impatrq/Protorp/Compras/Facturas de compra/20251116_184129.jpg

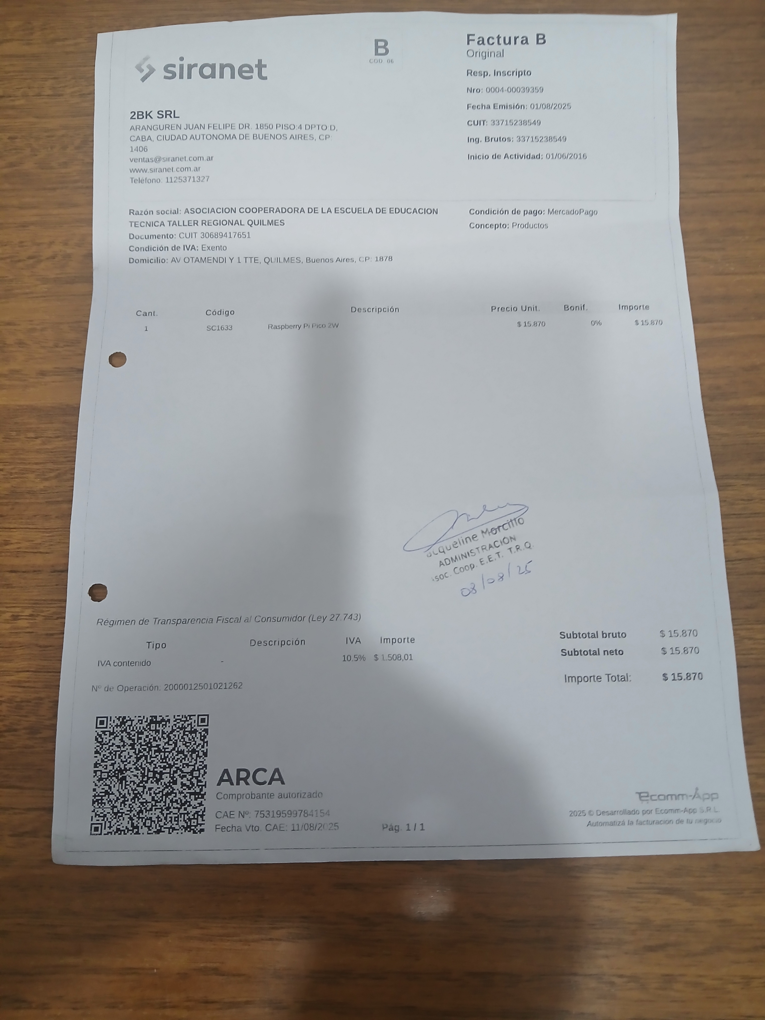
Compras/Facturas de compra/20251116_184129.jpg
