impatrq/Protorp/Compras/Facturas de compra/20251116_184212.jpg

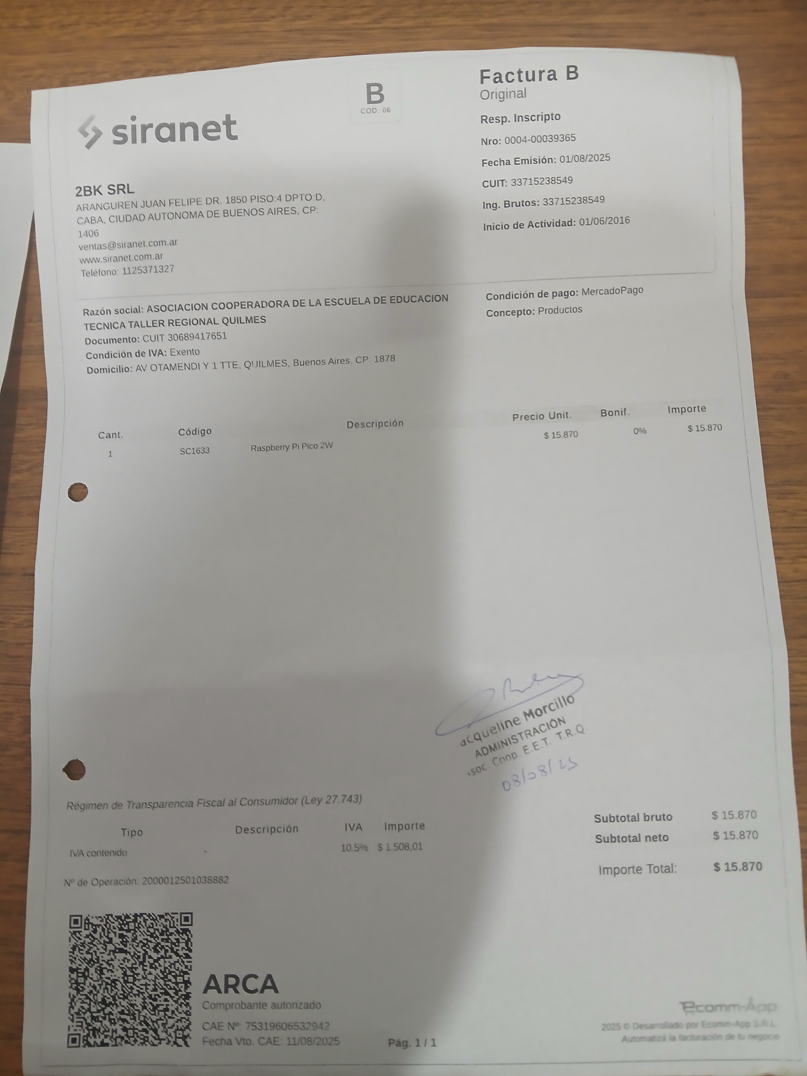
Compras/Facturas de compra/20251116_184212.jpg
