impatrq/Protorp/Compras/Facturas de compra/20251116_184254.jpg

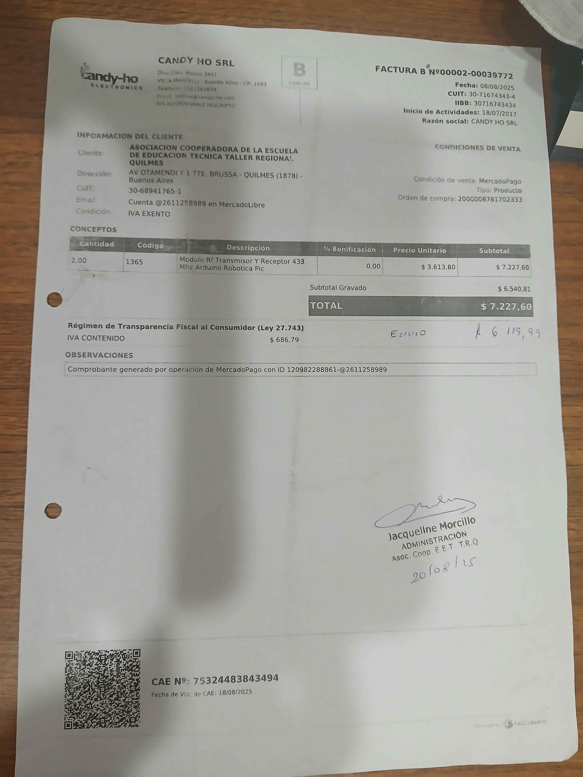
Compras/Facturas de compra/20251116_184254.jpg
