impatrq/Protorp/Compras/Facturas de compra/20251116_184328.jpg

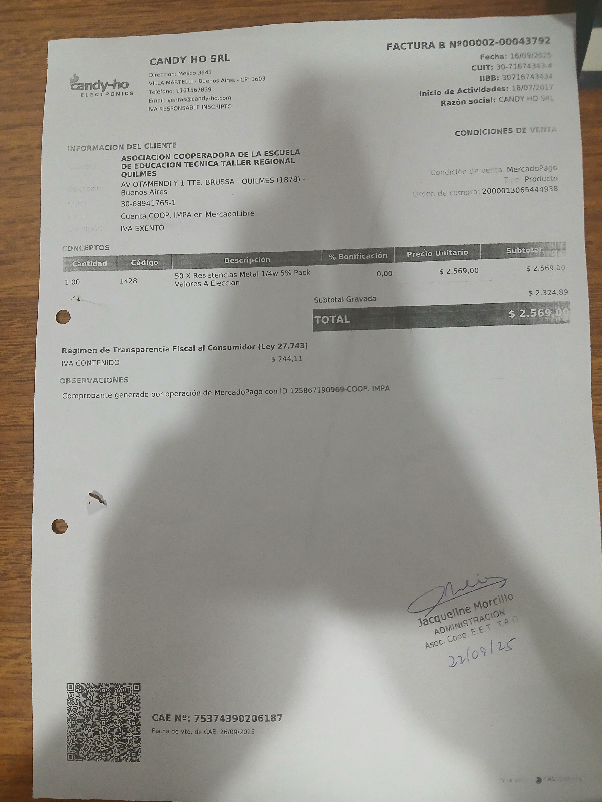
Compras/Facturas de compra/20251116_184328.jpg
