impatrq/Protorp/Compras/Facturas de compra/20251116_184347.jpg

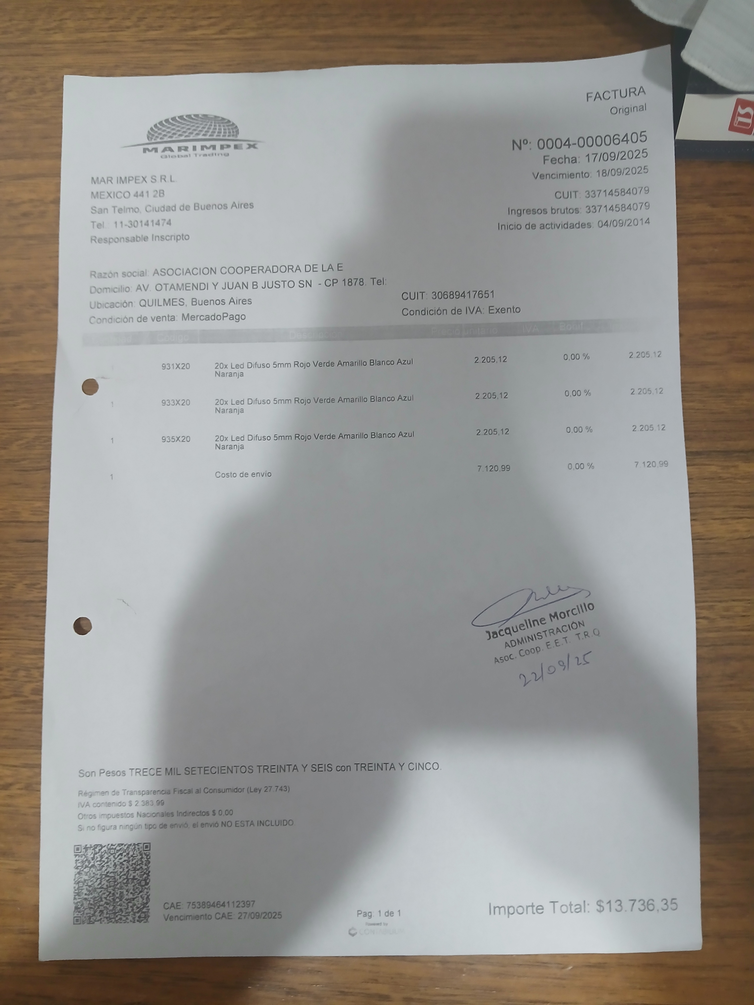
Compras/Facturas de compra/20251116_184347.jpg
