impatrq/Protorp/Compras/Facturas de compra/20251116_184413.jpg

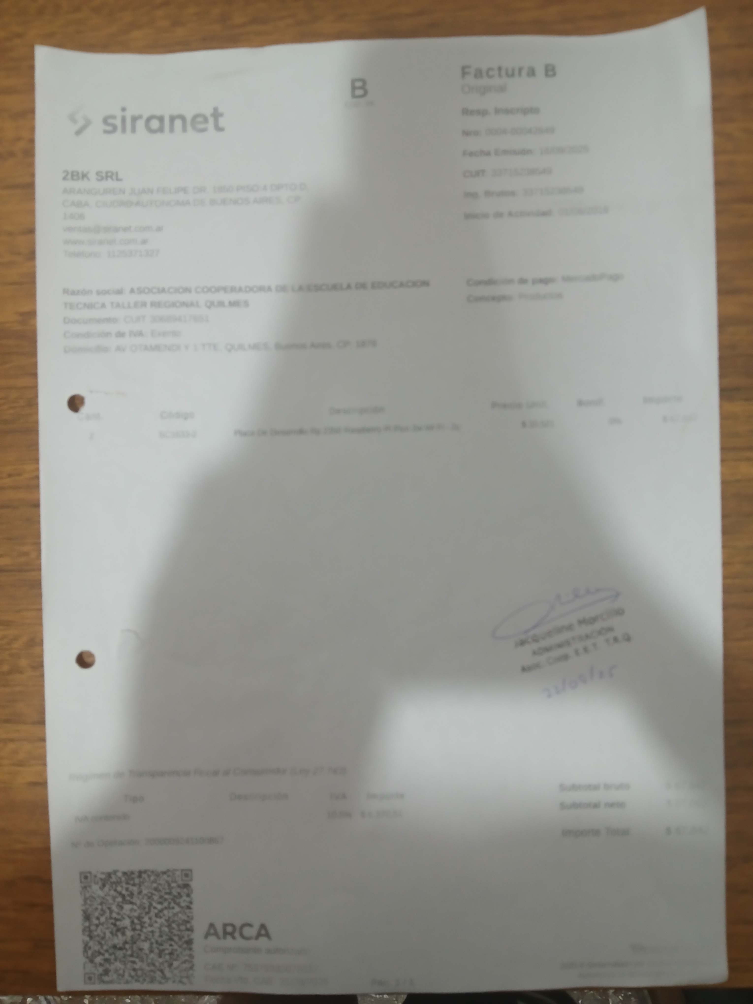
Compras/Facturas de compra/20251116_184413.jpg
