impatrq/Protorp/Compras/Facturas de compra/20251116_184430.jpg

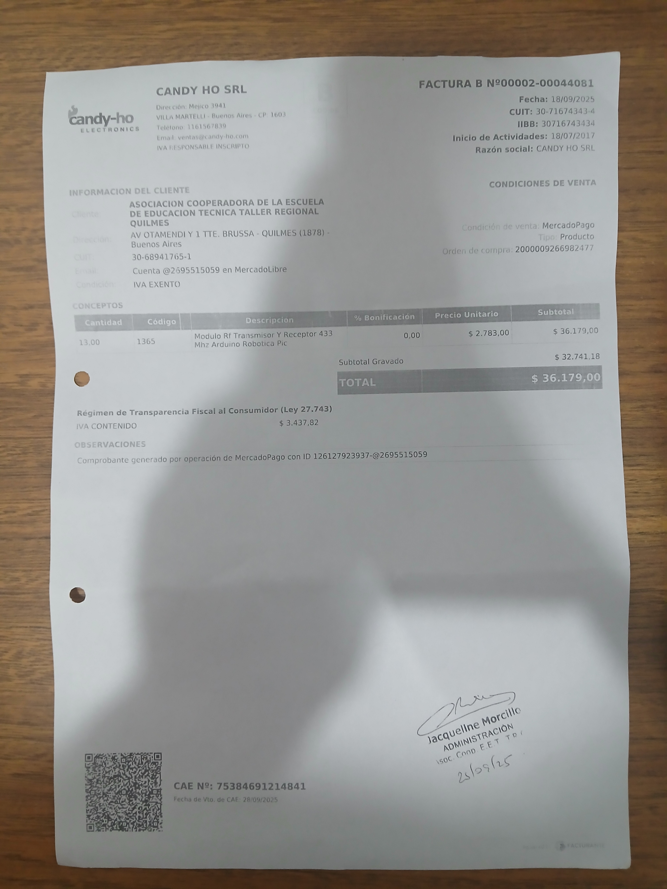
Compras/Facturas de compra/20251116_184430.jpg
