impatrq/Protorp/Compras/Facturas de compra/20251116_184449.jpg

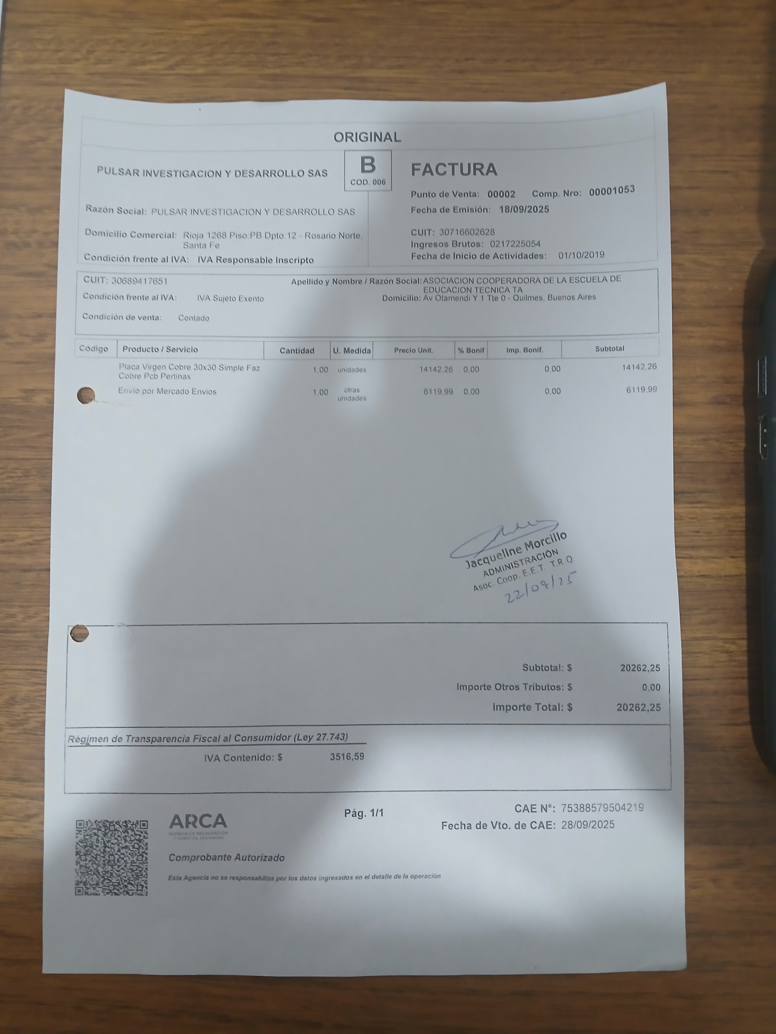
Compras/Facturas de compra/20251116_184449.jpg
