impatrq/Protorp/Compras/Facturas de compra/20251116_184504.jpg

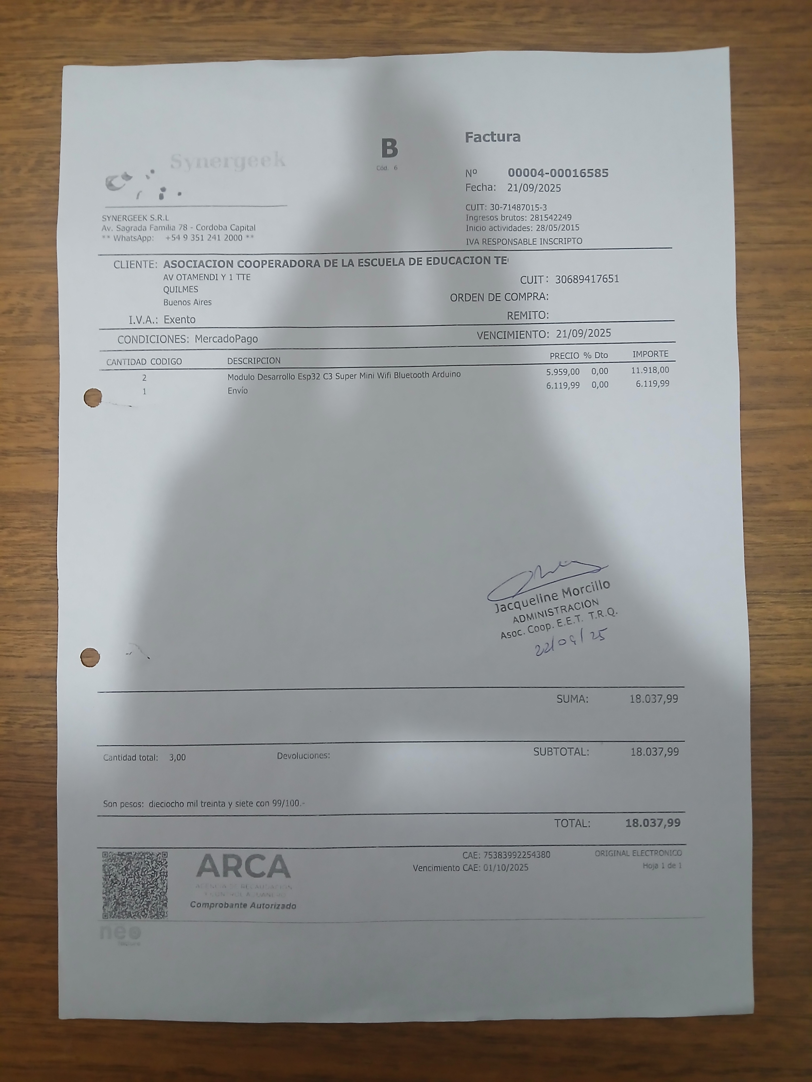
Compras/Facturas de compra/20251116_184504.jpg
