impatrq/Protorp/Compras/Facturas de compra/20251116_184520.jpg

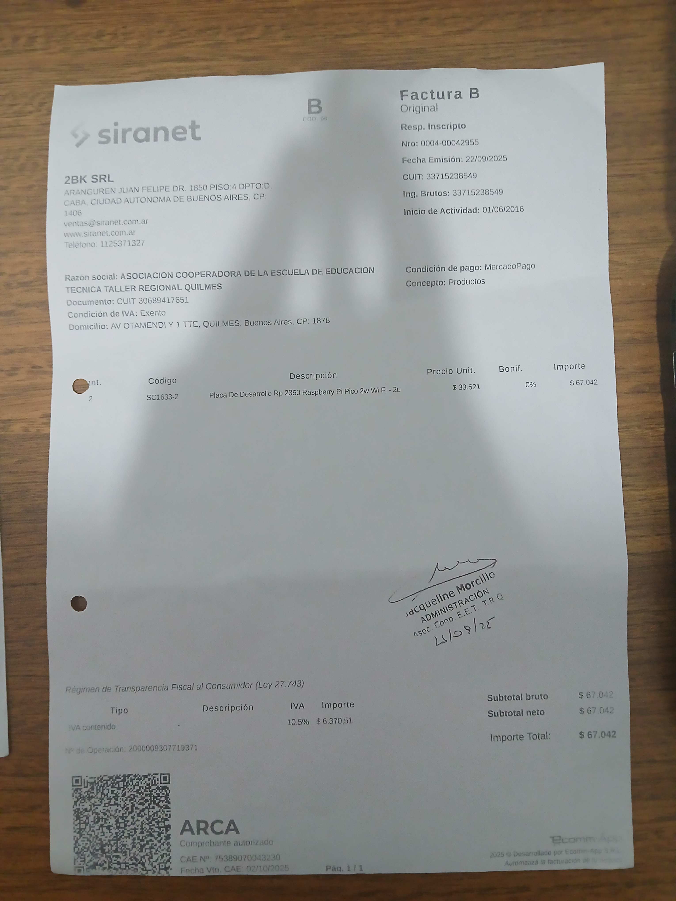
Compras/Facturas de compra/20251116_184520.jpg
