impatrq/Protorp/Compras/Facturas de compra/20251116_184534.jpg

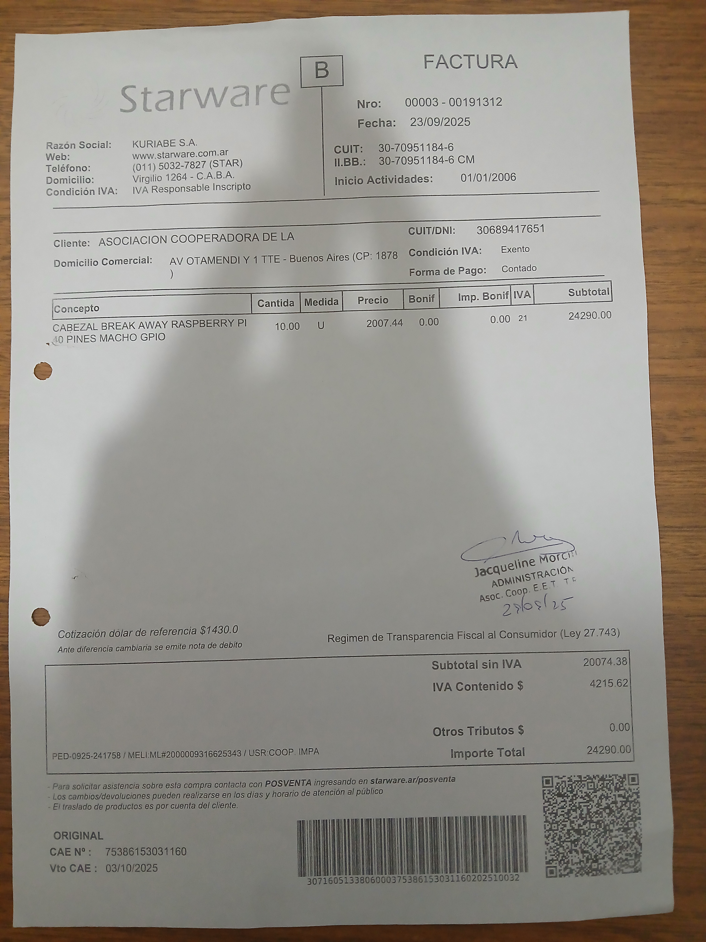
Compras/Facturas de compra/20251116_184534.jpg
