impatrq/Protorp/Equipo/CVs del equipo/CV - Joaquin.jpg

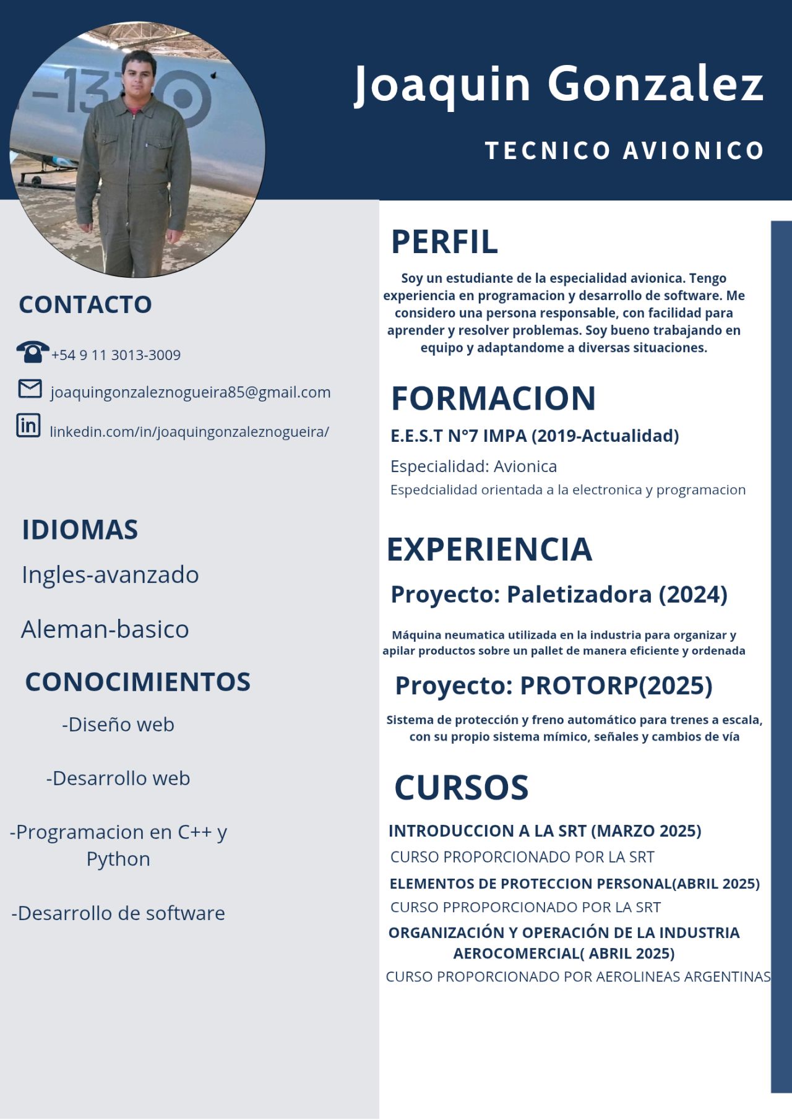
Equipo/CVs del equipo/CV - Joaquin.jpg
