impatrq/Protorp/Equipo/Foto del equipo/Foto del eqipo.jpeg

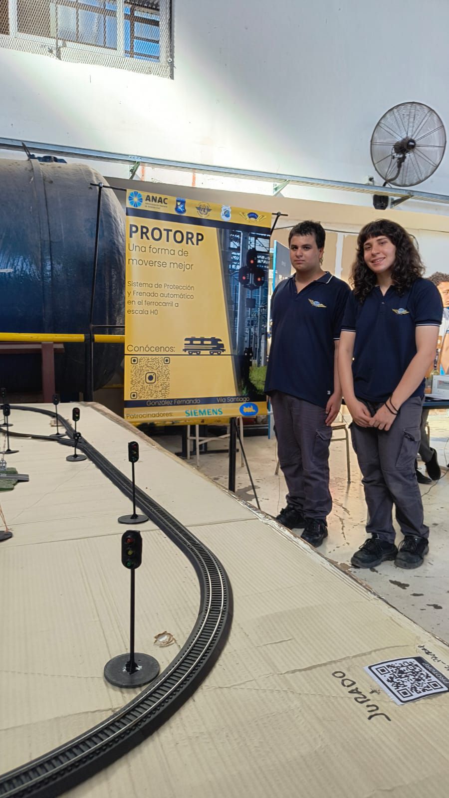
Equipo/Foto del equipo/Foto del eqipo.jpeg
