impatrq/Protorp/fotos/diagramas/prototipo 1 diagrama electrico.webp

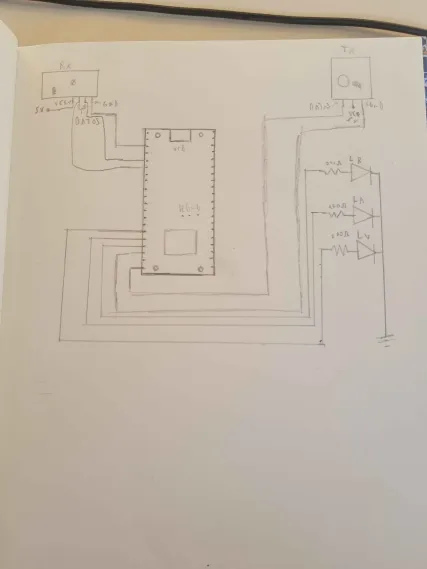
fotos/diagramas/prototipo 1 diagrama electrico.webp
