impatrq/Protorp/fotos/impresiones 3D/9bde5b57-a3d0-4a50-99e6-3efff3342a33.jpg

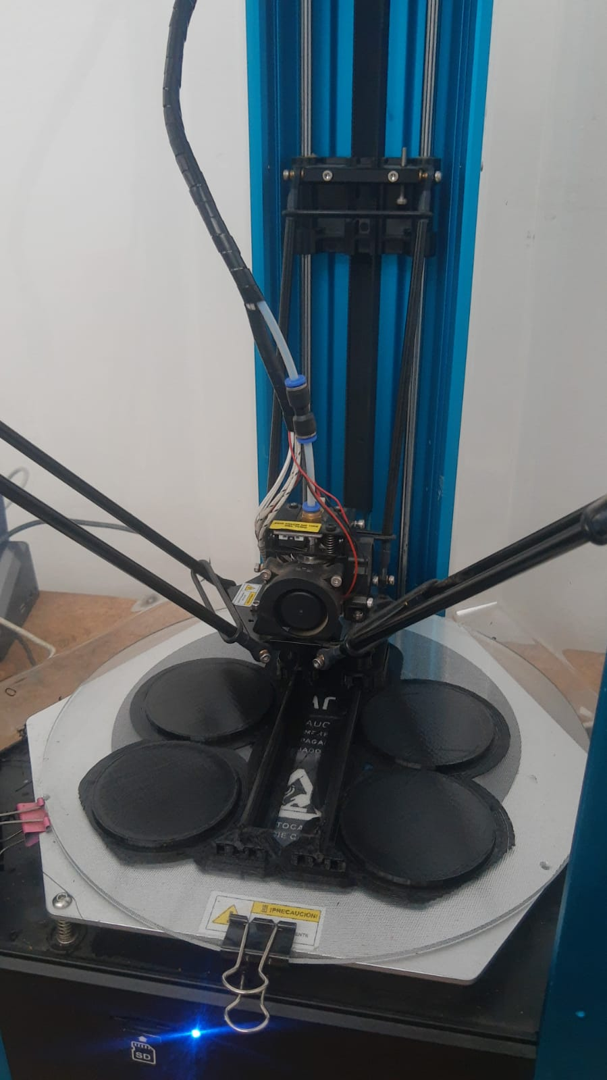
fotos/impresiones 3D/9bde5b57-a3d0-4a50-99e6-3efff3342a33.jpg
