impatrq/Protorp/fotos/impresiones 3D/df6539c7-ce4e-4fce-84c8-1d385a50d44c.jpg

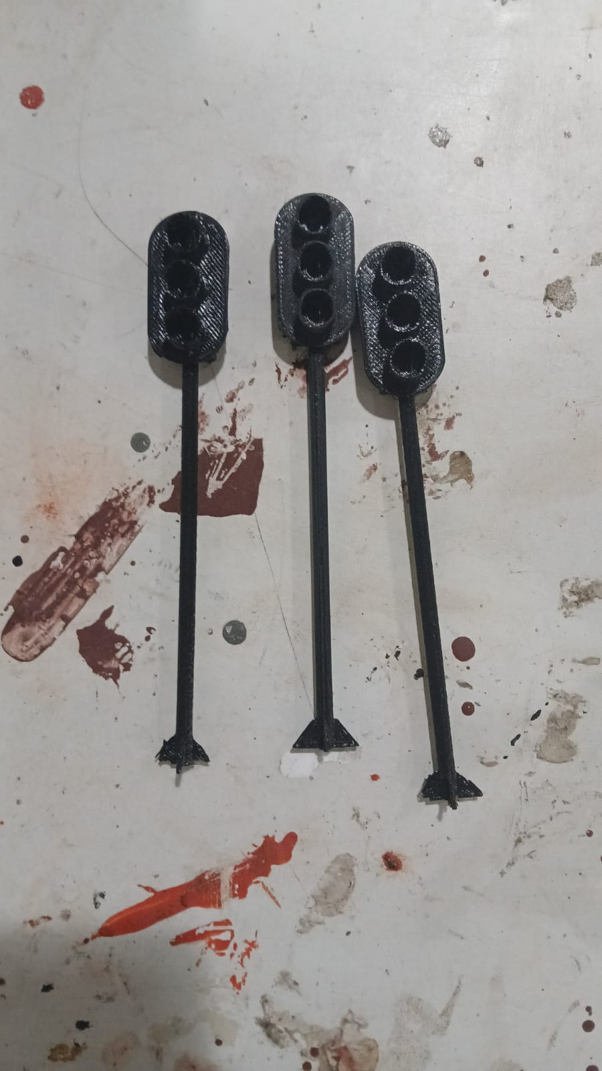
fotos/impresiones 3D/df6539c7-ce4e-4fce-84c8-1d385a50d44c.jpg
