impatrq/Protorp/fotos/Maqueta/IMG-20251118-WA0002.jpg

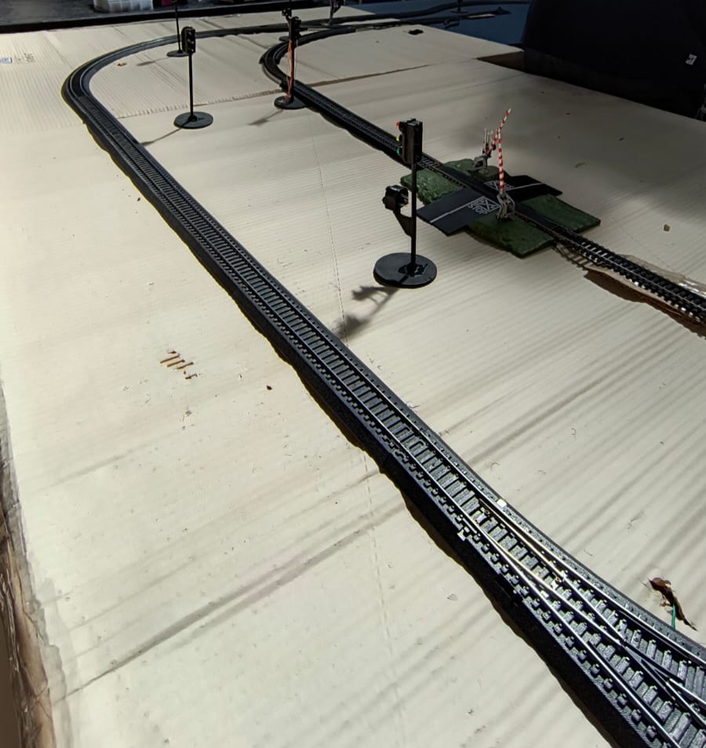
fotos/Maqueta/IMG-20251118-WA0002.jpg
