impatrq/Protorp/fotos/Maqueta/IMG-20251118-WA0003.jpg

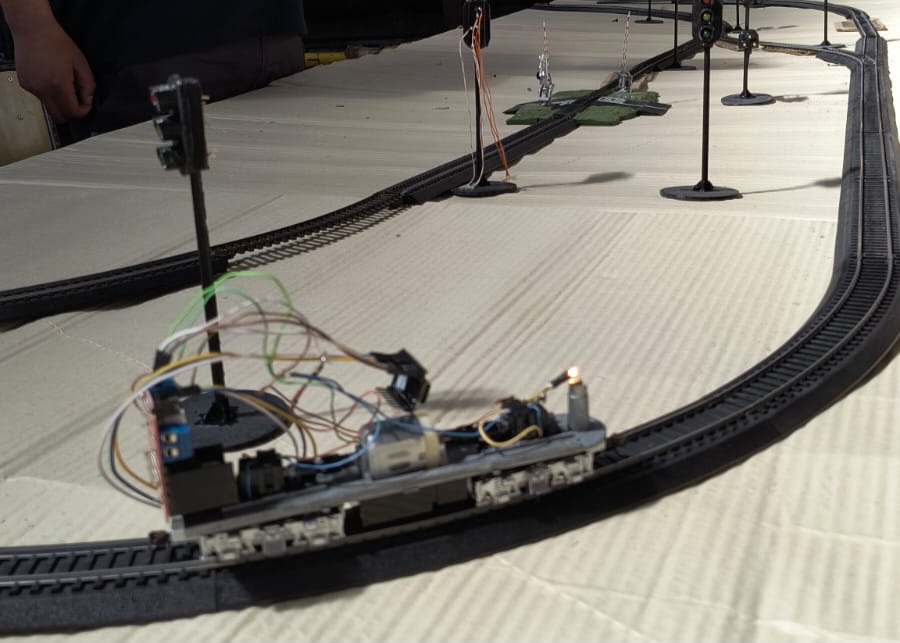
fotos/Maqueta/IMG-20251118-WA0003.jpg
