impatrq/Protorp/fotos/Maqueta/IMG-20251118-WA0004.jpg

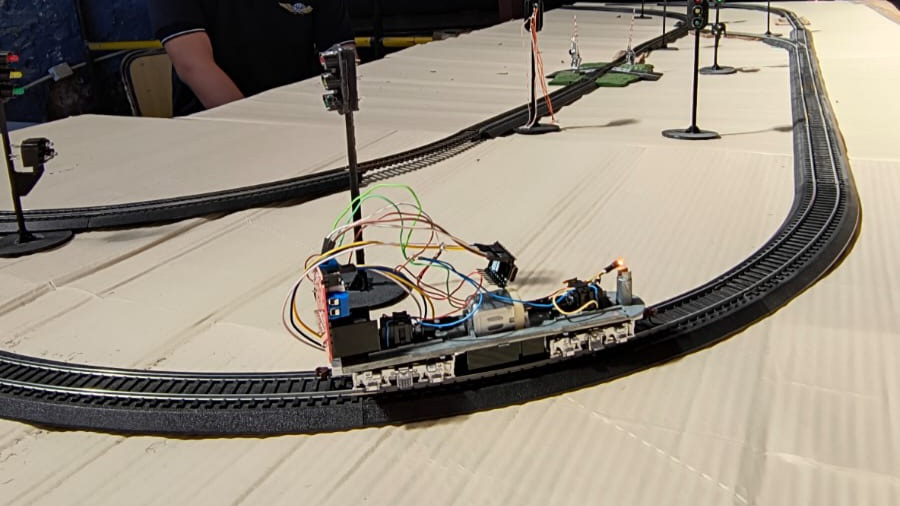
fotos/Maqueta/IMG-20251118-WA0004.jpg
