impatrq/Protorp/fotos/placas de cobre/6936b12a-9ef0-415d-9e3a-1d418f14f2b1.jpg

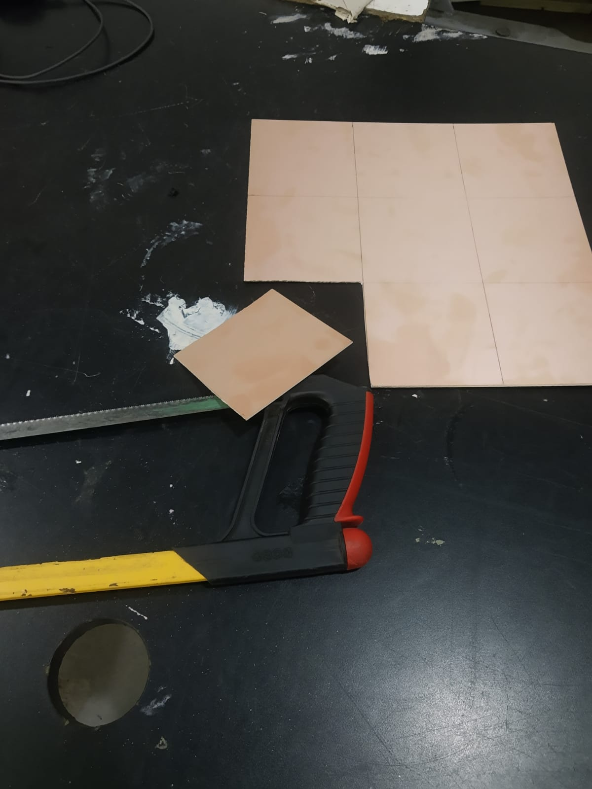
fotos/placas de cobre/6936b12a-9ef0-415d-9e3a-1d418f14f2b1.jpg
