impatrq/Protorp/fotos/placas de cobre/2706066d-67e2-4fa1-b246-8f61f098e9b2.jpg

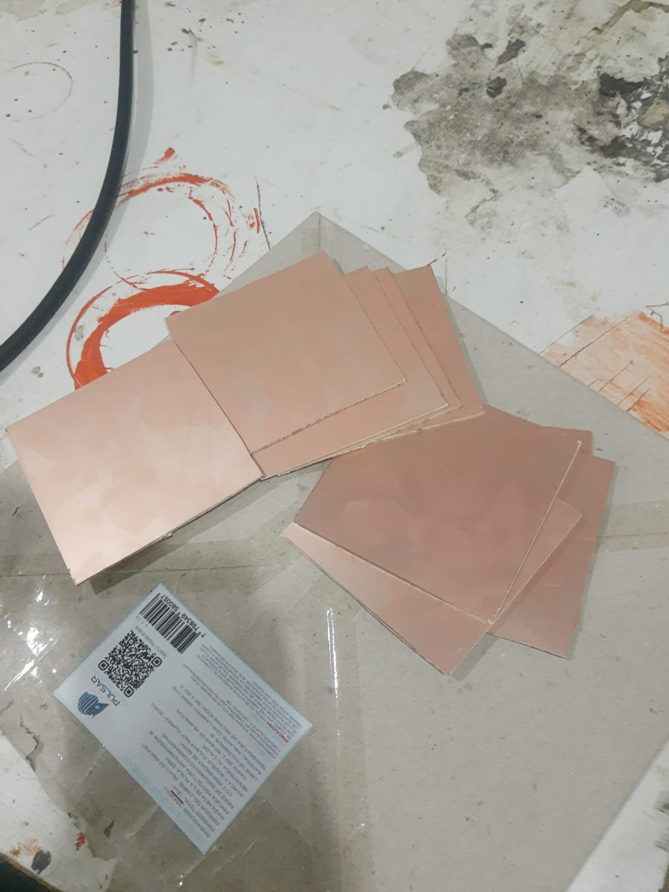
fotos/placas de cobre/2706066d-67e2-4fa1-b246-8f61f098e9b2.jpg
