impatrq/Protorp/pagina web/fondo 2.jpeg

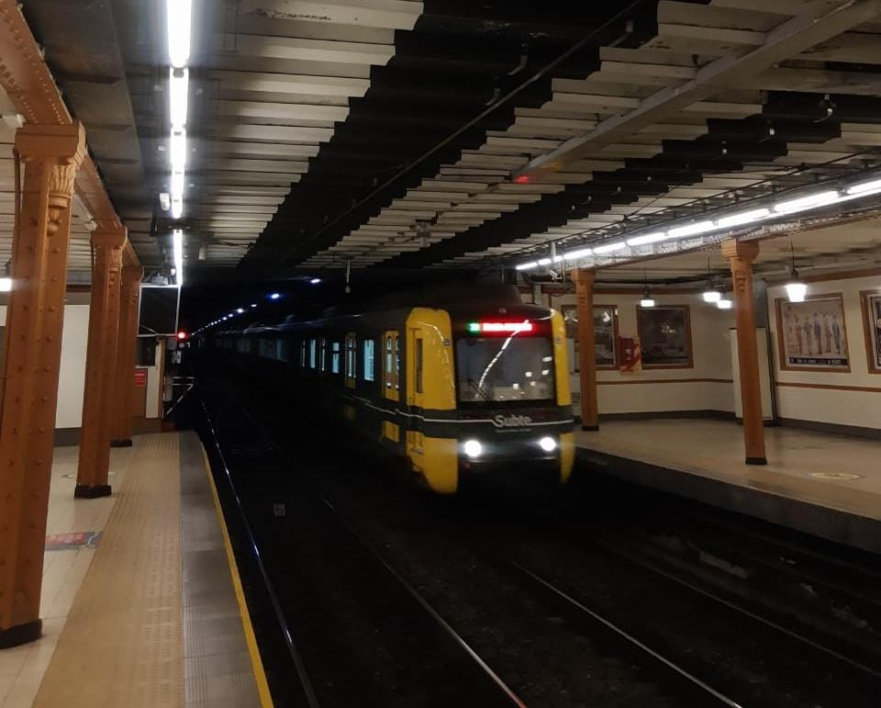
pagina web/fondo 2.jpeg
