impatrq/Protorp/pagina web/fondo 3.jpeg

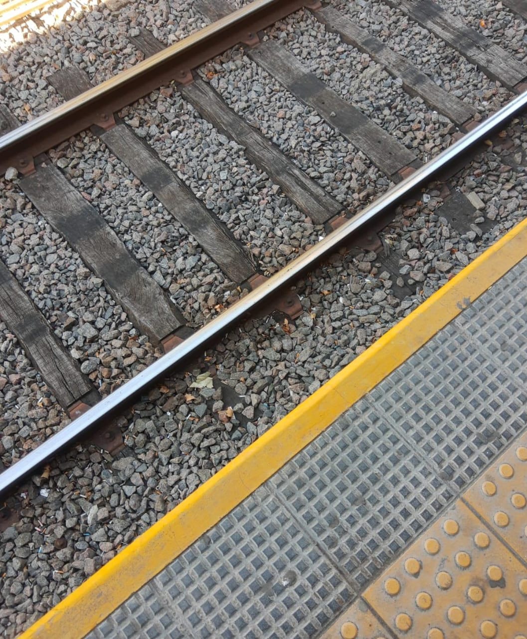
pagina web/fondo 3.jpeg
