impatrq/Protorp/pagina web/fondo.jpg

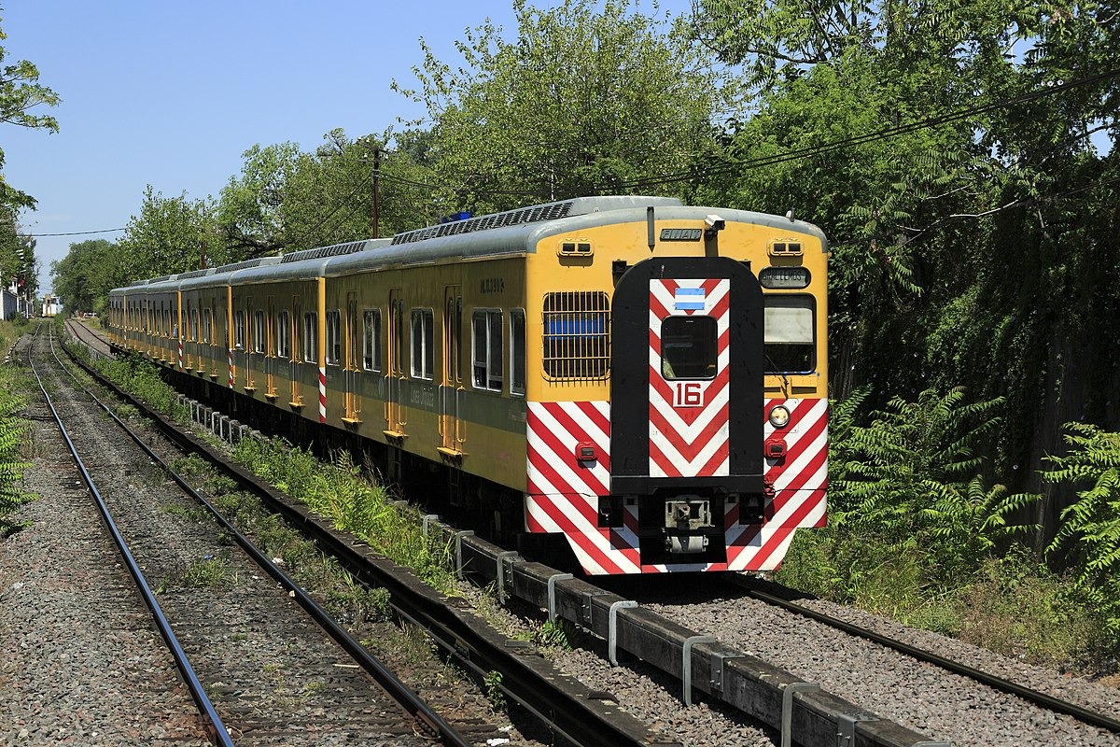
pagina web/fondo.jpg
