impatrq/Protorp/fotos/pruebas en protoboard/prueba con una sola señal/4f3c9ad4-0f97-4569-8ee4-096b7872f10b.jpg

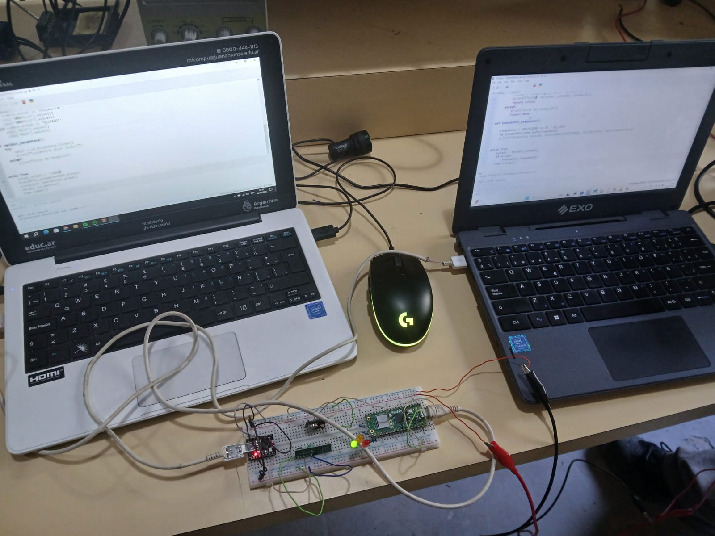
fotos/pruebas en protoboard/prueba con una sola señal/4f3c9ad4-0f97-4569-8ee4-096b7872f10b.jpg
