impatrq/Protorp/fotos/pruebas en protoboard/prueba con una sola señal/pruebas con 2 señales/0c9b6ed5-34d7-45da-a39e-0842129c3650.jpg

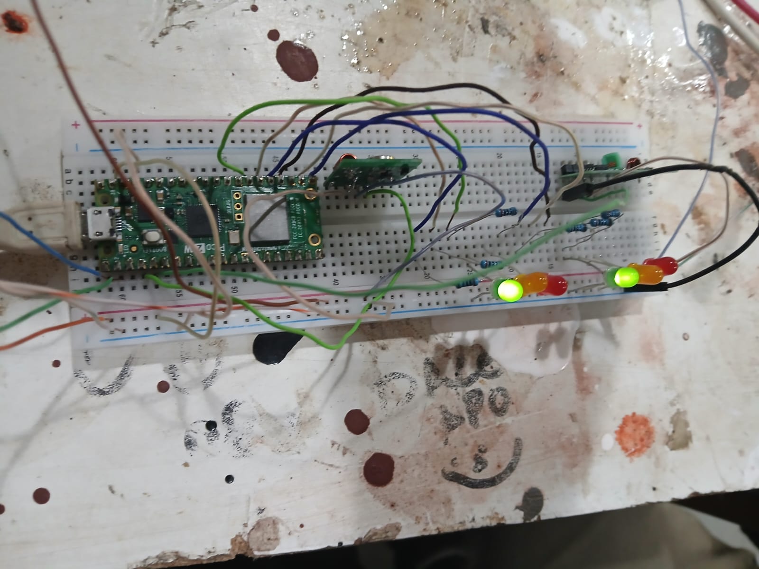
fotos/pruebas en protoboard/prueba con una sola señal/pruebas con 2 señales/0c9b6ed5-34d7-45da-a39e-0842129c3650.jpg
