impatrq/Protorp/fotos/pruebas en protoboard/prueba con una sola señal/pruebas con 2 señales/2c0518c5-a413-42dd-a2f3-44a652915057.jpg

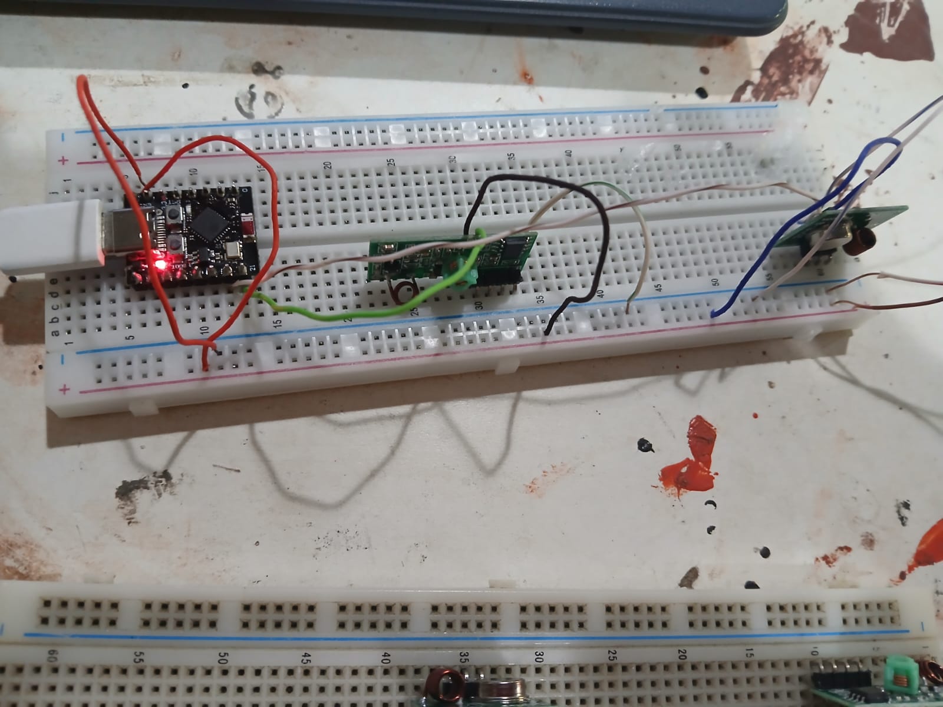
fotos/pruebas en protoboard/prueba con una sola señal/pruebas con 2 señales/2c0518c5-a413-42dd-a2f3-44a652915057.jpg
