impatrq/Protorp/fotos/pruebas en protoboard/prueba con una sola señal/pruebas con 2 señales/5c336b47-350f-4e57-b789-9494cb5c7c3b.jpg

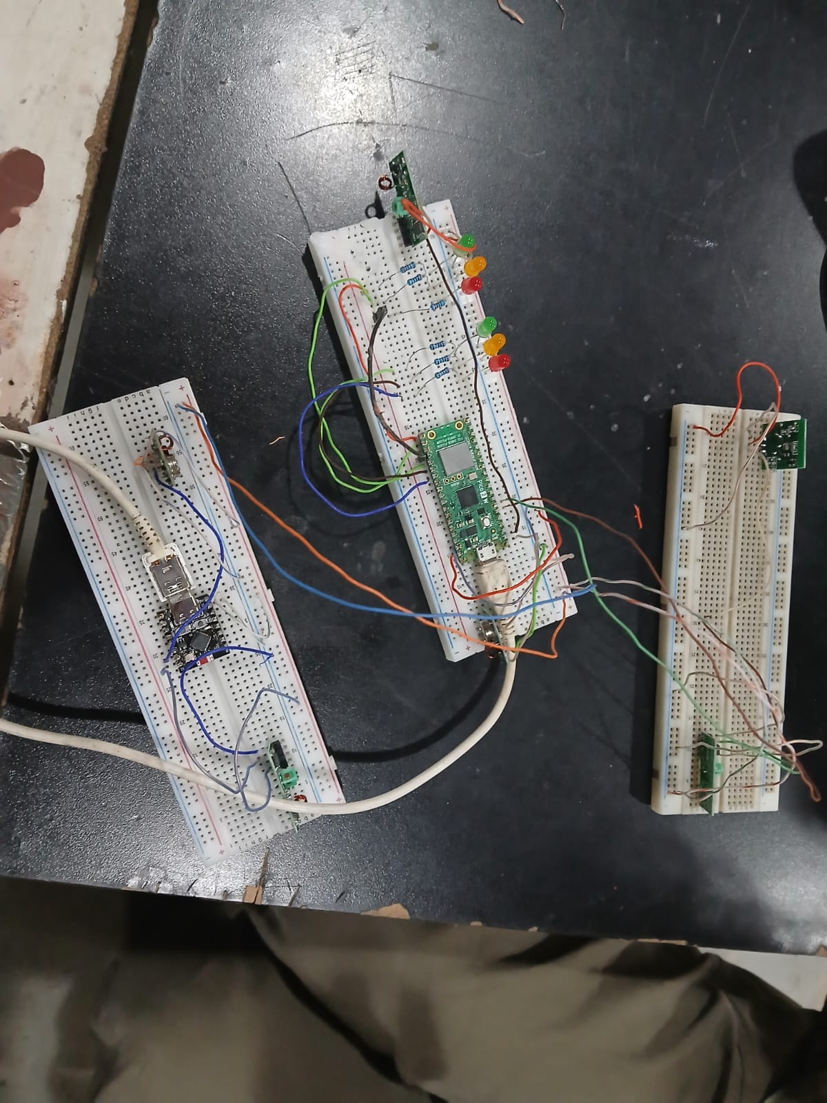
fotos/pruebas en protoboard/prueba con una sola señal/pruebas con 2 señales/5c336b47-350f-4e57-b789-9494cb5c7c3b.jpg
