impatrq/Protorp/fotos/pruebas en protoboard/prueba con una sola señal/pruebas con 2 señales/b4aca771-4e02-4c60-abcc-8e24a5026f2d.jpg

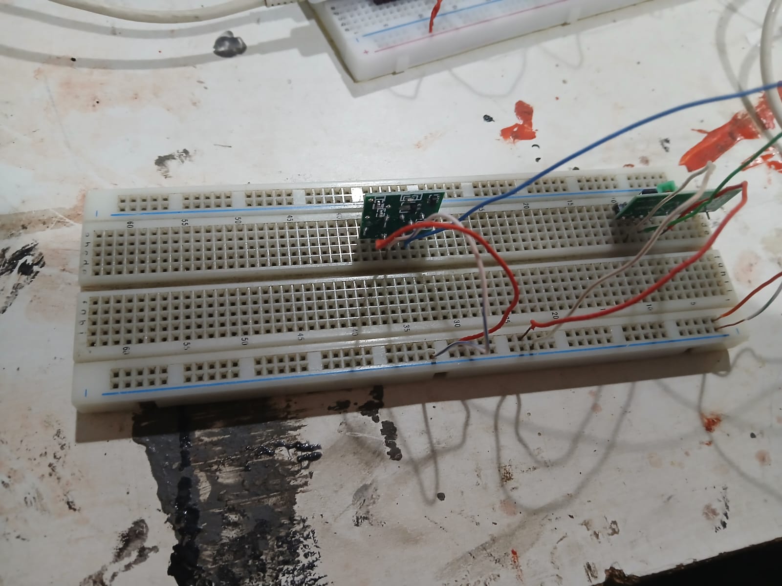
fotos/pruebas en protoboard/prueba con una sola señal/pruebas con 2 señales/b4aca771-4e02-4c60-abcc-8e24a5026f2d.jpg
