impatrq/Protorp/fotos/pruebas en protoboard/prueba con una sola señal/pruebas con 2 señales/d7d8d0da-7930-4166-92d5-eda0d52ef679.jpg

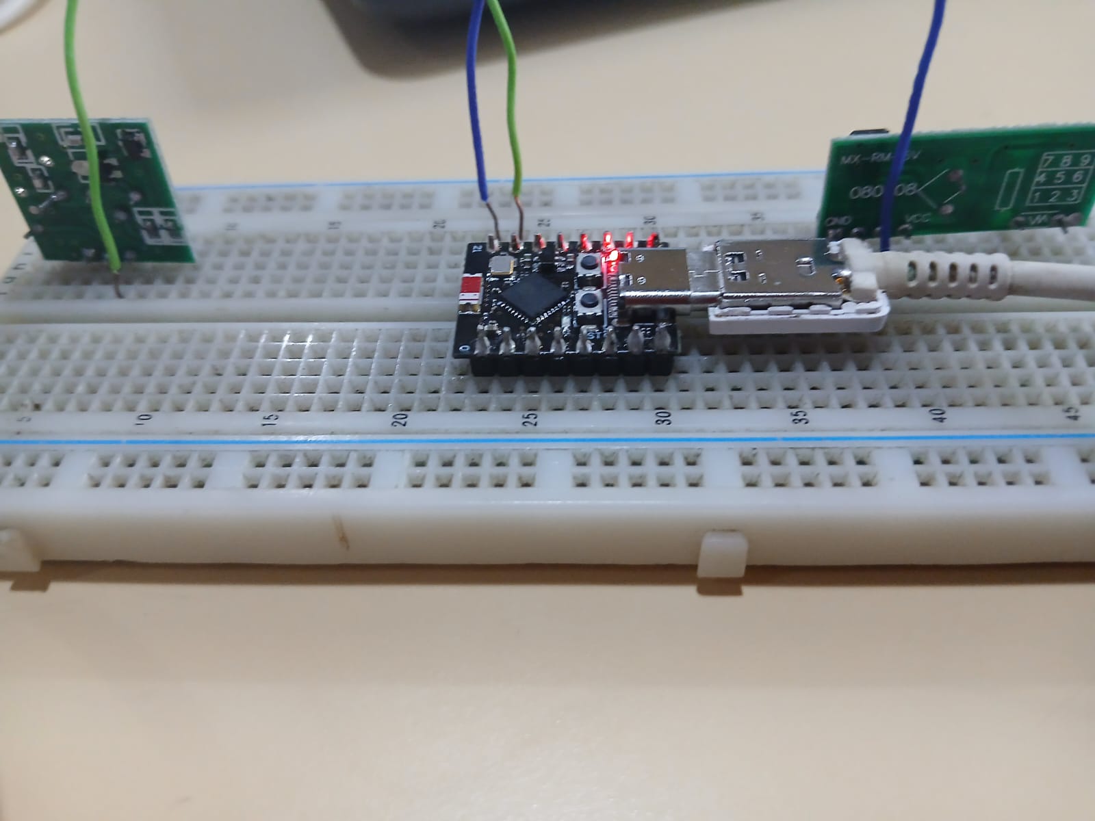
fotos/pruebas en protoboard/prueba con una sola señal/pruebas con 2 señales/d7d8d0da-7930-4166-92d5-eda0d52ef679.jpg
