impatrq/Protorp/KiCad/Esquematico de las placas.kicad_sch

## KiCad design KiCad/Esquematico de las placas.kicad_sch (2025-10-13)

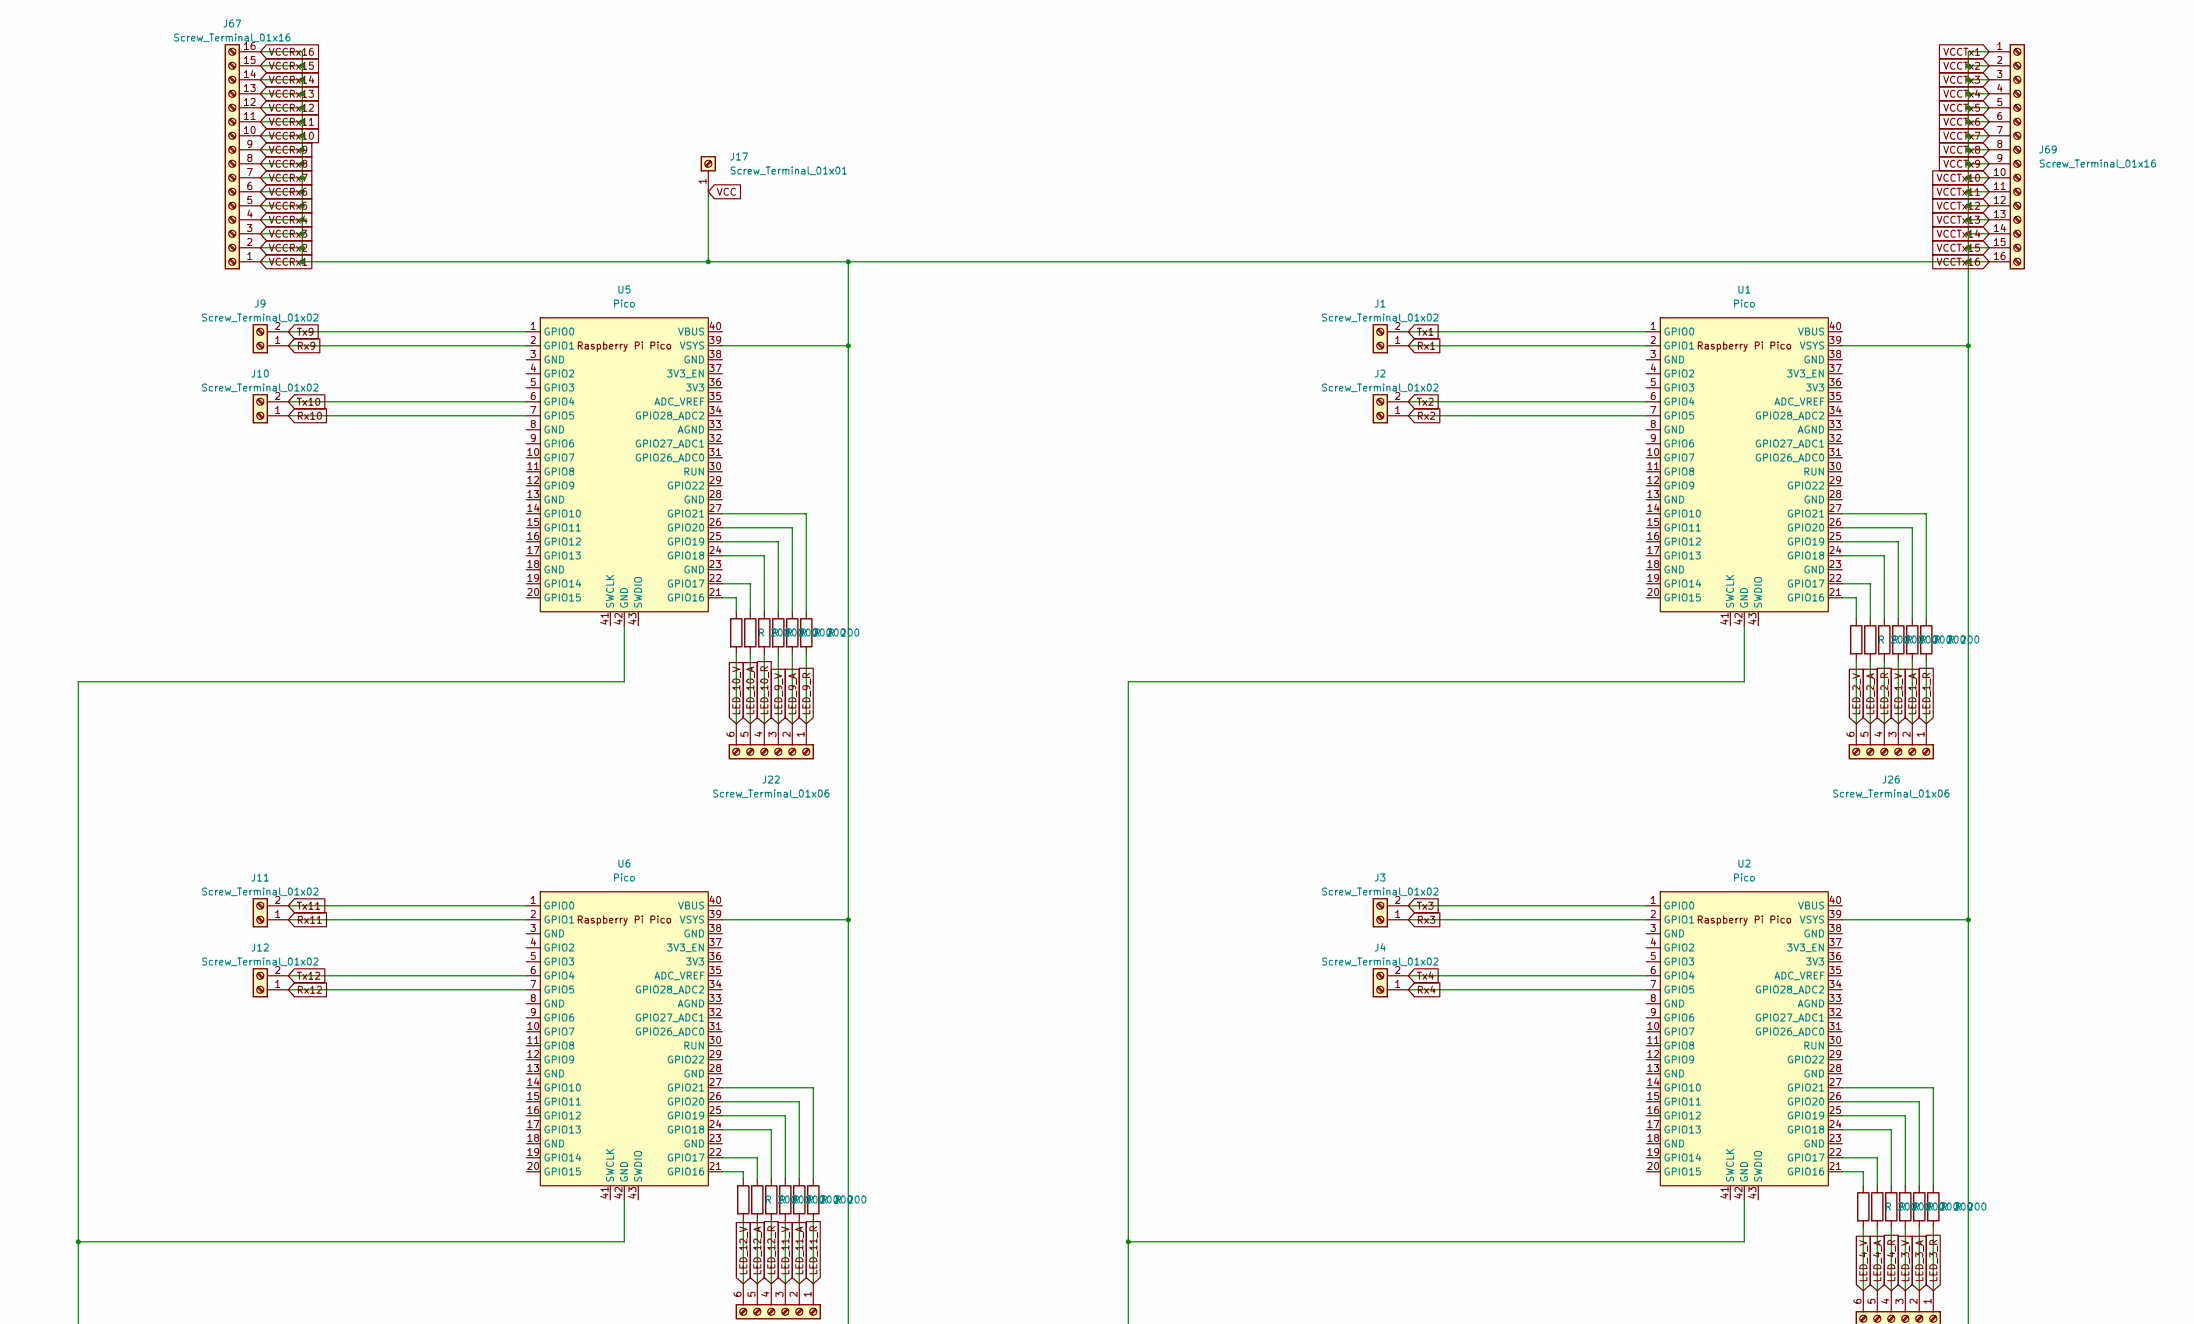
[picture p71: schematic Esquematico de las placas.kicad_sch, part in row 1, column 1]

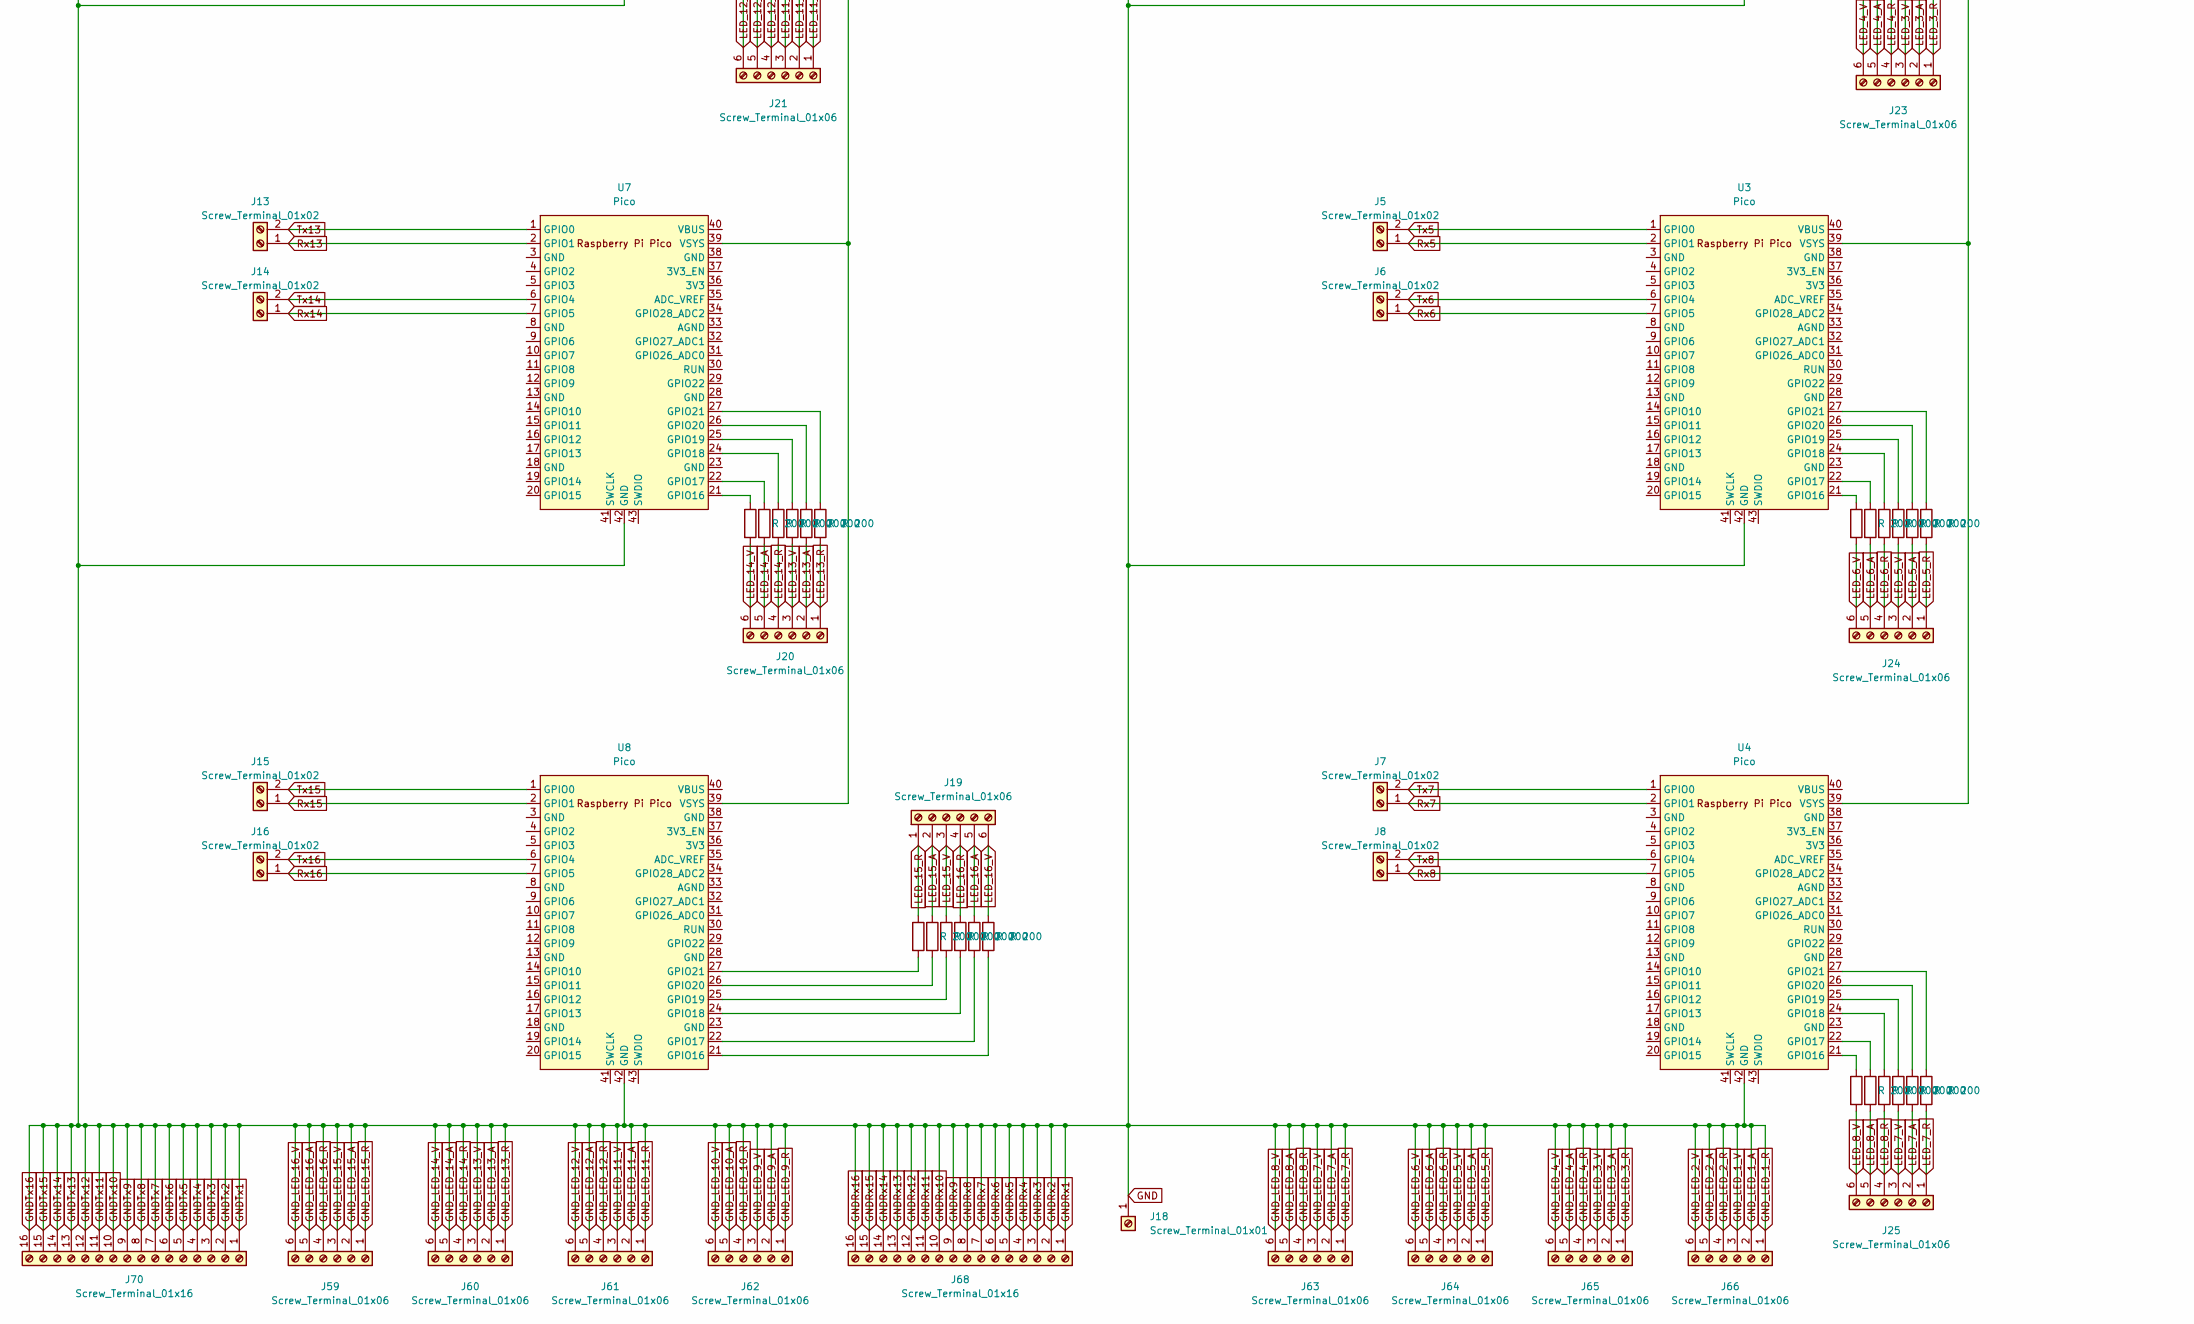
[picture p72: schematic Esquematico de las placas.kicad_sch, part in row 2, column 1]

Parts:
J1, J2, J3, J4, J5, J6, J7, J8, J9, J10, J11, J12, J13, J14, J15, J16: Screw_Terminal_01x02; TerminalBlock_bornier-2_P5.08mm
J17, J18: Screw_Terminal_01x01; TerminalBlock_Degson_DG250-3.5-01P_1x01_P3.50mm_45Degree
J19, J20, J21, J22, J23, J24, J25, J26, J59, J60, J61, J62, J63, J64, J65, J66: Screw_Terminal_01x06; TerminalBlock_bornier-6_P5.08mm
J67, J68, J69, J70: Screw_Terminal_01x16; TerminalBlock_Xinya_XY308-2.54-16P_1x16_P2.54mm_Horizontal
R1, R2, R3, R4, R5, R6, R7, R8, R9, R10, R11, R12, R13, R14, R15, R16, R17, R18, R19, R20, R21, R22, R23, R24, R25, R26, R27, R28, R29, R30, R31, R32, R33, R34, R35, R36, R37, R38, R39, R40, R41, R42, R44, R45, R46, R47, R48, R49: R 200; R_Axial_DIN0204_L3.6mm_D1.6mm_P5.08mm_Horizontal
U1, U2, U3, U4, U5, U6, U7, U8: Pico; RPi_Pico_SMD_TH

Connections:
GND: J18.1, J59.1, J59.2, J59.3, J59.4, J59.5, J59.6, J60.1, J60.2, J60.3, J60.4, J60.5, J60.6, J61.1, J61.2, J61.3, J61.4, J61.5, J61.6, J62.1, J62.2, J62.3, J62.4, J62.5, J62.6, J63.1, J63.2, J63.3, J63.4, J63.5, J63.6, J64.1, J64.2, J64.3, J64.4, J64.5, J64.6, J65.1, J65.2, J65.3, J65.4, J65.5, J65.6, J66.1, J66.2, J66.3, J66.4, J66.5, J66.6, J68.1, J68.2, J68.3, J68.4, J68.5, J68.6, J68.7, J68.8, J68.9, J68.10, J68.11, J68.12, J68.13, J68.14, J68.15, J68.16, J70.1, J70.2, J70.3, J70.4, J70.5, J70.6, J70.7, J70.8, J70.9, J70.10, J70.11, J70.12, J70.13, J70.14, J70.15, J70.16, U1.42 (GND), U2.42 (GND), U3.42 (GND), U4.42 (GND), U5.42 (GND), U6.42 (GND), U7.42 (GND), U8.42 (GND)
LED_1_A: J26.2, R48.2
LED_1_R: J26.1, R49.2
LED_1_V: J26.3, R47.2
LED_2_A: J26.5, R45.2
LED_2_R: J26.4, R46.2
LED_2_V: J26.6, R44.2
LED_3_A: J23.2, R5.2
LED_3_R: J23.1, R6.2
LED_3_V: J23.3, R4.2
LED_4_A: J23.5, R2.2
LED_4_R: J23.4, R3.2
LED_4_V: J23.6, R1.2
LED_5_A: J24.2, R11.2
LED_5_R: J24.1, R12.2
LED_5_V: J24.3, R10.2
LED_6_A: J24.5, R8.2
LED_6_R: J24.4, R9.2
LED_6_V: J24.6, R7.2
LED_7_A: J25.2, R17.2
LED_7_R: J25.1, R18.2
LED_7_V: J25.3, R16.2
LED_8_A: J25.5, R14.2
LED_8_R: J25.4, R15.2
LED_8_V: J25.6, R13.2
LED_9_A: J22.2, R41.2
LED_9_R: J22.1, R42.2
LED_9_V: J22.3, R40.2
LED_10_A: J22.5, R38.2
LED_10_R: J22.4, R39.2
LED_10_V: J22.6, R37.2
LED_11_A: J21.2, R35.2
LED_11_R: J21.1, R36.2
LED_11_V: J21.3, R34.2
LED_12_A: J21.5, R32.2
LED_12_R: J21.4, R33.2
LED_12_V: J21.6, R31.2
LED_13_A: J20.2, R29.2
LED_13_R: J20.1, R30.2
LED_13_V: J20.3, R28.2
LED_14_A: J20.5, R26.2
LED_14_R: J20.4, R27.2
LED_14_V: J20.6, R25.2
LED_15_A: J19.2, R20.1
LED_15_R: J19.1, R19.1
LED_15_V: J19.3, R21.1
LED_16_A: J19.5, R23.1
LED_16_R: J19.4, R22.1
LED_16_V: J19.6, R24.1
unnamed: R1.1, U2.21 (GPIO16)
unnamed: R2.1, U2.22 (GPIO17)
unnamed: R3.1, U2.24 (GPIO18)
unnamed: R4.1, U2.25 (GPIO19)
unnamed: R5.1, U2.26 (GPIO20)
unnamed: R6.1, U2.27 (GPIO21)
unnamed: R7.1, U3.21 (GPIO16)
unnamed: R8.1, U3.22 (GPIO17)
unnamed: R9.1, U3.24 (GPIO18)
unnamed: R10.1, U3.25 (GPIO19)
unnamed: R11.1, U3.26 (GPIO20)
unnamed: R12.1, U3.27 (GPIO21)
unnamed: R13.1, U4.21 (GPIO16)
unnamed: R14.1, U4.22 (GPIO17)
unnamed: R15.1, U4.24 (GPIO18)
unnamed: R16.1, U4.25 (GPIO19)
unnamed: R17.1, U4.26 (GPIO20)
unnamed: R18.1, U4.27 (GPIO21)
unnamed: R19.2, U8.27 (GPIO21)
unnamed: R20.2, U8.26 (GPIO20)
unnamed: R21.2, U8.25 (GPIO19)
unnamed: R22.2, U8.24 (GPIO18)
unnamed: R23.2, U8.22 (GPIO17)
unnamed: R24.2, U8.21 (GPIO16)
unnamed: R25.1, U7.21 (GPIO16)
unnamed: R26.1, U7.22 (GPIO17)
unnamed: R27.1, U7.24 (GPIO18)
unnamed: R28.1, U7.25 (GPIO19)
unnamed: R29.1, U7.26 (GPIO20)
unnamed: R30.1, U7.27 (GPIO21)
unnamed: R31.1, U6.21 (GPIO16)
unnamed: R32.1, U6.22 (GPIO17)
unnamed: R33.1, U6.24 (GPIO18)
unnamed: R34.1, U6.25 (GPIO19)
unnamed: R35.1, U6.26 (GPIO20)
unnamed: R36.1, U6.27 (GPIO21)
unnamed: R37.1, U5.21 (GPIO16)
unnamed: R38.1, U5.22 (GPIO17)
unnamed: R39.1, U5.24 (GPIO18)
unnamed: R40.1, U5.25 (GPIO19)
unnamed: R41.1, U5.26 (GPIO20)
unnamed: R42.1, U5.27 (GPIO21)
unnamed: R44.1, U1.21 (GPIO16)
unnamed: R45.1, U1.22 (GPIO17)
unnamed: R46.1, U1.24 (GPIO18)
unnamed: R47.1, U1.25 (GPIO19)
unnamed: R48.1, U1.26 (GPIO20)
unnamed: R49.1, U1.27 (GPIO21)
Rx1: J1.1, U1.2 (GPIO1)
Rx2: J2.1, U1.7 (GPIO5)
Rx3: J3.1, U2.2 (GPIO1)
Rx4: J4.1, U2.7 (GPIO5)
Rx5: J5.1, U3.2 (GPIO1)
Rx6: J6.1, U3.7 (GPIO5)
Rx7: J7.1, U4.2 (GPIO1)
Rx8: J8.1, U4.7 (GPIO5)
Rx9: J9.1, U5.2 (GPIO1)
Rx10: J10.1, U5.7 (GPIO5)
Rx11: J11.1, U6.2 (GPIO1)
Rx12: J12.1, U6.7 (GPIO5)
Rx13: J13.1, U7.2 (GPIO1)
Rx14: J14.1, U7.7 (GPIO5)
Rx15: J15.1, U8.2 (GPIO1)
Rx16: J16.1, U8.7 (GPIO5)
Tx1: J1.2, U1.1 (GPIO0)
Tx2: J2.2, U1.6 (GPIO4)
Tx3: J3.2, U2.1 (GPIO0)
Tx4: J4.2, U2.6 (GPIO4)
Tx5: J5.2, U3.1 (GPIO0)
Tx6: J6.2, U3.6 (GPIO4)
Tx7: J7.2, U4.1 (GPIO0)
Tx8: J8.2, U4.6 (GPIO4)
Tx9: J9.2, U5.1 (GPIO0)
Tx10: J10.2, U5.6 (GPIO4)
Tx11: J11.2, U6.1 (GPIO0)
Tx12: J12.2, U6.6 (GPIO4)
Tx13: J13.2, U7.1 (GPIO0)
Tx14: J14.2, U7.6 (GPIO4)
Tx15: J15.2, U8.1 (GPIO0)
Tx16: J16.2, U8.6 (GPIO4)
VCC: J17.1, J67.1, J67.2, J67.3, J67.4, J67.5, J67.6, J67.7, J67.8, J67.9, J67.10, J67.11, J67.12, J67.13, J67.14, J67.15, J67.16, J69.1, J69.2, J69.3, J69.4, J69.5, J69.6, J69.7, J69.8, J69.9, J69.10, J69.11, J69.12, J69.13, J69.14, J69.15, J69.16, U1.39 (VSYS), U2.39 (VSYS), U3.39 (VSYS), U4.39 (VSYS), U5.39 (VSYS), U6.39 (VSYS), U7.39 (VSYS), U8.39 (VSYS)
